reid23/yet-another-pompfen-store/build/components/guard_epp.dxf

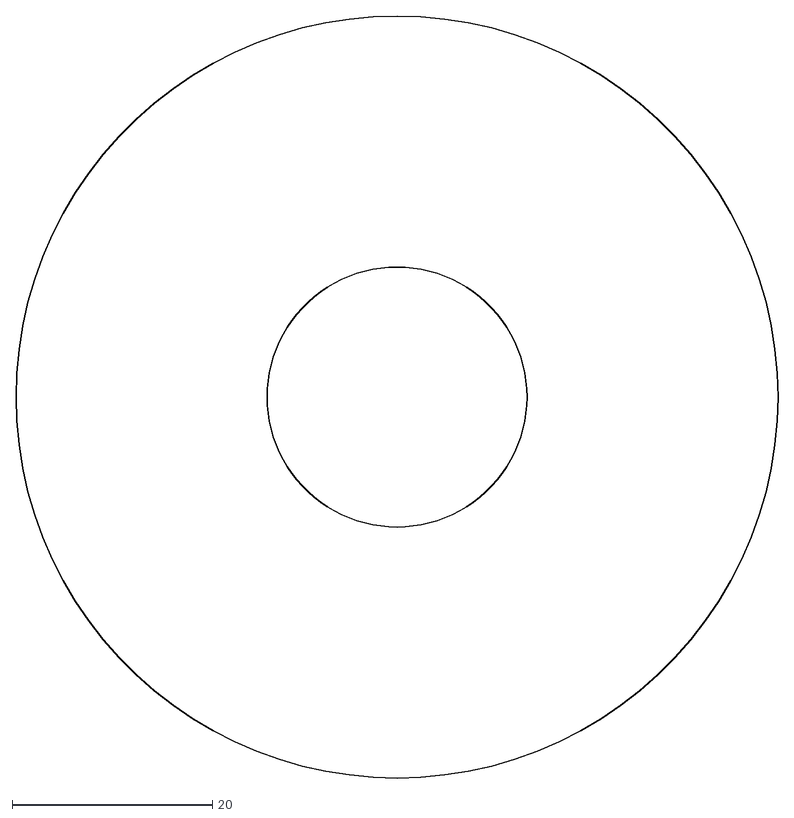
[picture p41: CAD file, 2026-06-17]
build/components/guard_epp.dxf
76.2 x 76.2
