reid23/yet-another-pompfen-store/build/components/tip_cap.stl

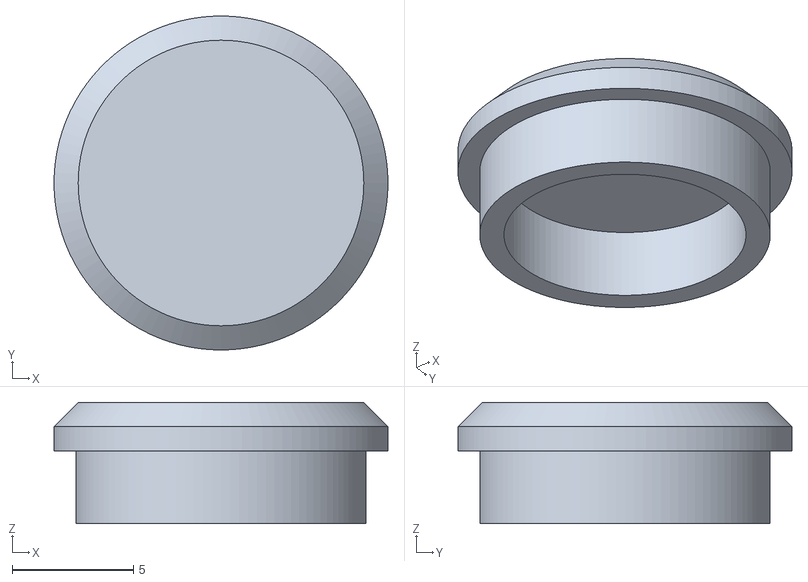
[picture p42: CAD file, 2026-06-17]
build/components/tip_cap.stl
13.8 x 13.8 x 5.00
