reid23/yet-another-pompfen-store/build/extras/guard_collet.stl

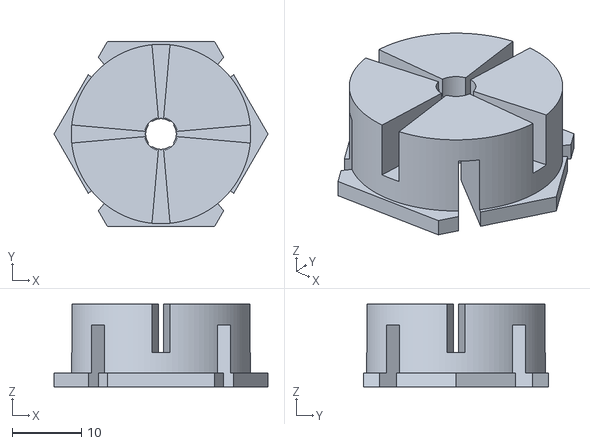
[picture p43: CAD file, 2026-07-21]
build/extras/guard_collet.stl
31.0 x 26.8 x 12.0
