reid23/yet-another-pompfen-store/build/components/blade_epp_foamside.dxf

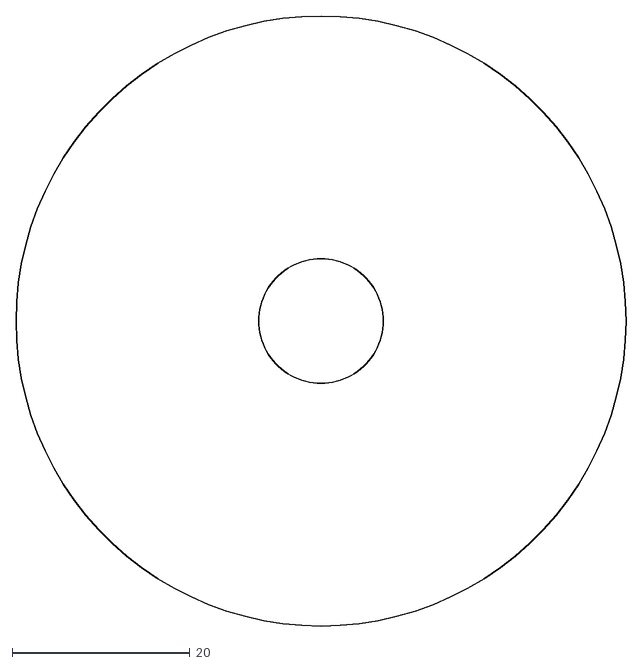
[picture p44: CAD file, 2026-06-17]
build/components/blade_epp_foamside.dxf
68.6 x 68.6
