reid23/yet-another-pompfen-store/build/extras/blade_foamside_collet.stl

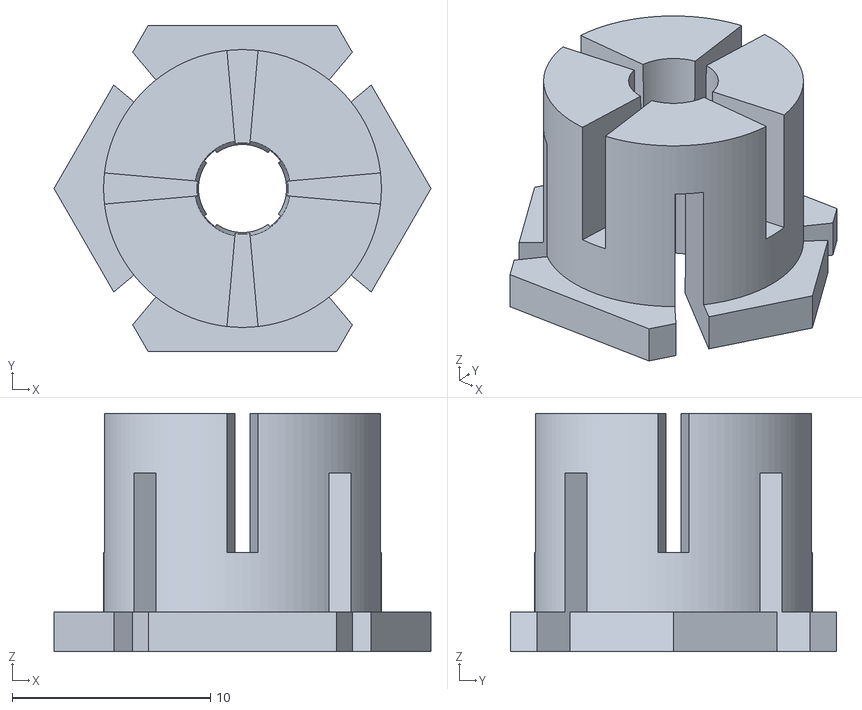
[picture p45: CAD file, 2026-07-21]
build/extras/blade_foamside_collet.stl
19.0 x 16.5 x 12.0
