reid23/yet-another-pompfen-store/build/components/tip_epp_radial.dxf

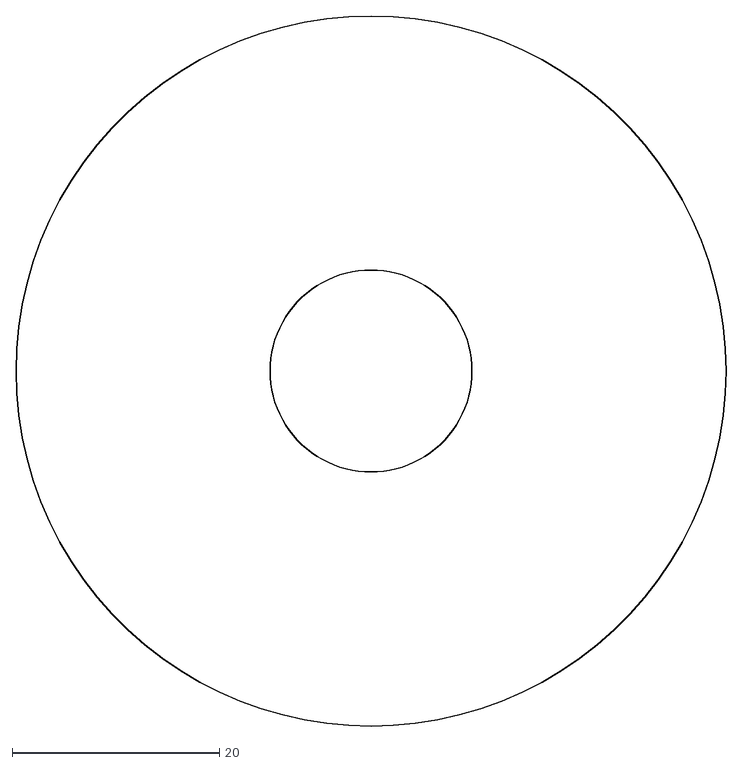
[picture p46: CAD file, 2026-06-17]
build/components/tip_epp_radial.dxf
68.6 x 68.6
