reid23/yet-another-pompfen-store/build/extras/fatigue_jig_bumper.stl

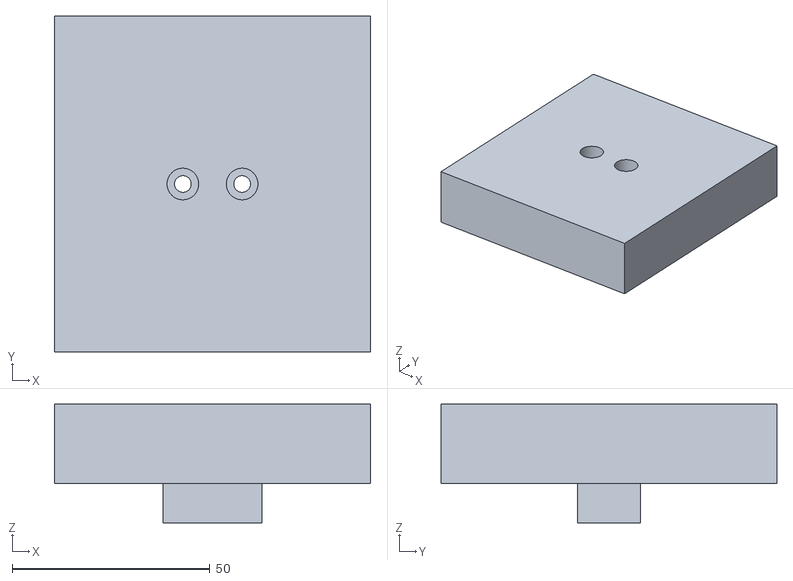
[picture p47: CAD file, 2026-07-21]
build/extras/fatigue_jig_bumper.stl
80.0 x 85.0 x 30.0
