reid23/yet-another-pompfen-store/build/components/collet.stl

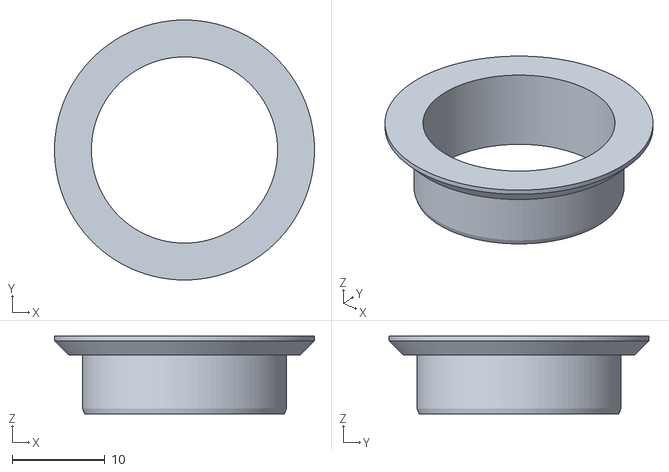
[picture p48: CAD file, 2026-06-17]
build/components/collet.stl
28.0 x 28.0 x 8.35
