reid23/yet-another-pompfen-store/build/extras/fatigue_jig_sample_mount.stl

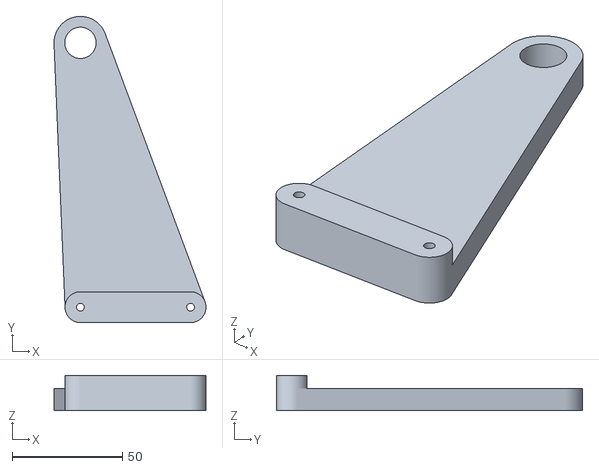
[picture p49: CAD file, 2026-07-21]
build/extras/fatigue_jig_sample_mount.stl
69.0 x 139.0 x 16.0
