reid23/yet-another-pompfen-store/build/components/tip_epp_axial.dxf

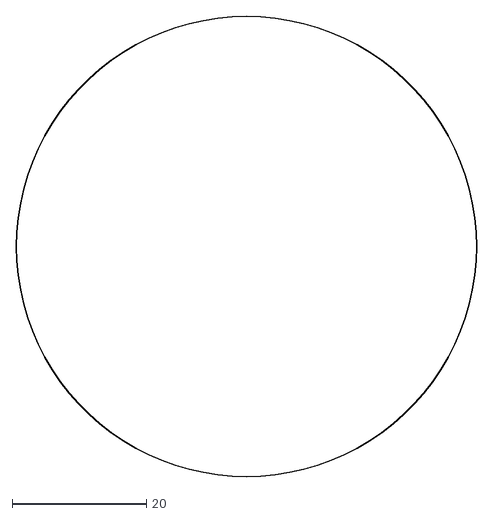
[picture p50: CAD file, 2026-06-17]
build/components/tip_epp_axial.dxf
68.6 x 68.6
