reid23/yet-another-pompfen-store/build/extras/tip_collet.stl

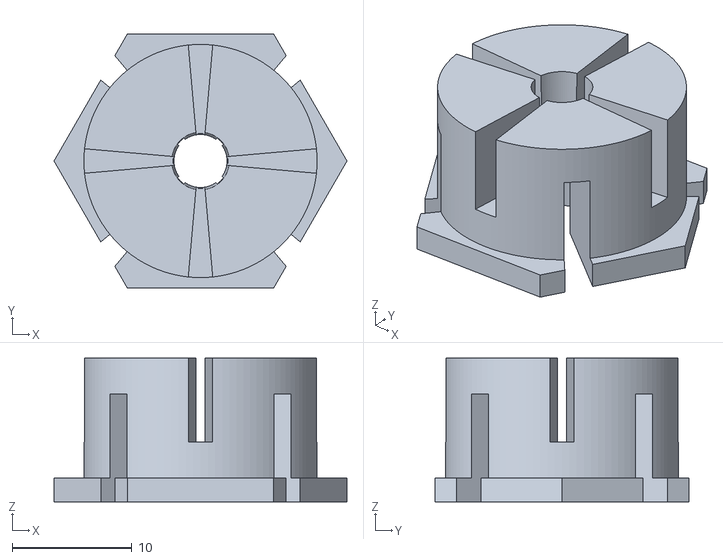
[picture p51: CAD file, 2026-07-21]
build/extras/tip_collet.stl
24.5 x 21.2 x 12.0
