reid23/yet-another-pompfen-store/build/components/pommel.stl

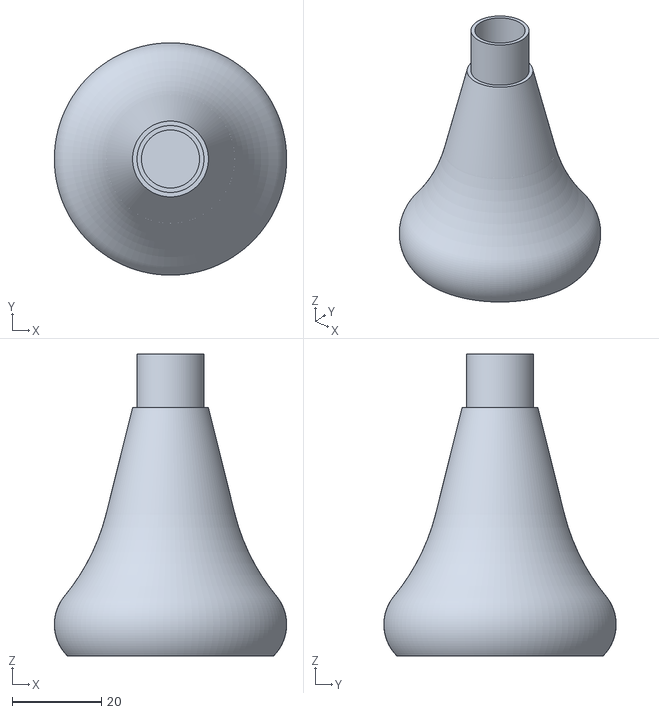
[picture p52: CAD file, 2026-03-15]
build/components/pommel.stl
52.1 x 52.1 x 67.7
