reid23/yet-another-pompfen-store/build/extras/fatigue_jig_strain_guage_mount.stl

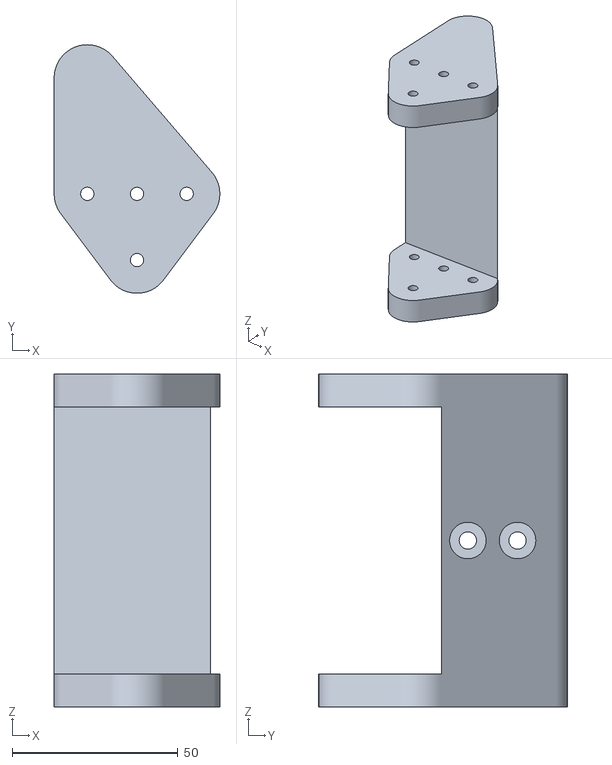
[picture p53: CAD file, 2026-07-21]
build/extras/fatigue_jig_strain_guage_mount.stl
50.0 x 75.0 x 100.5
