reid23/yet-another-pompfen-store/build/components/staff_grip.stl

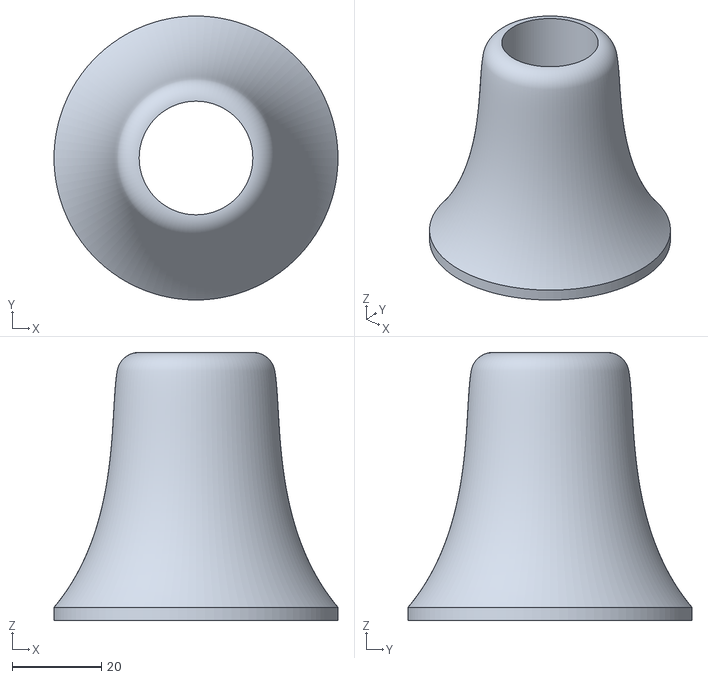
[picture p54: CAD file, 2026-02-28]
build/components/staff_grip.stl
63.5 x 63.5 x 60.0
