reid23/yet-another-pompfen-store/build/extras/blade_handside_collet.stl

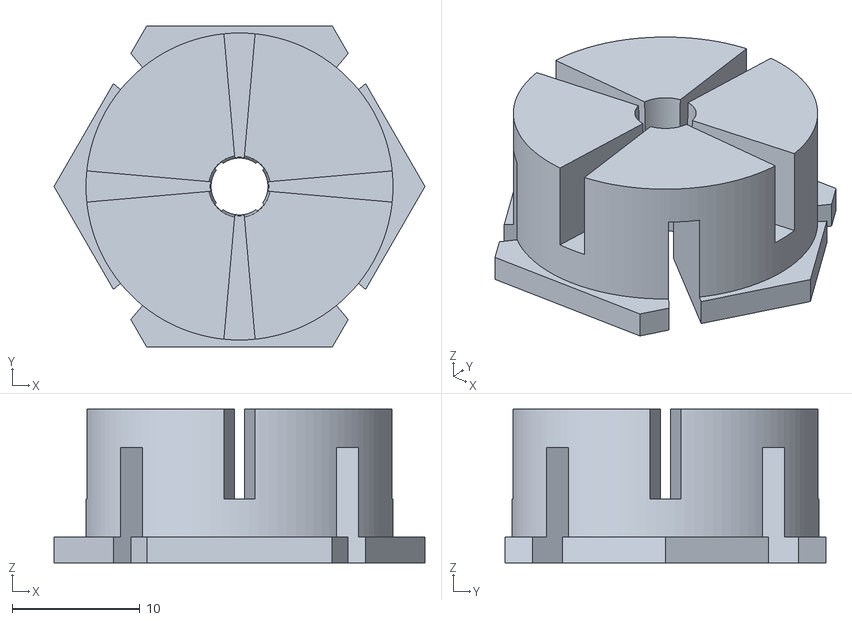
[picture p55: CAD file, 2026-07-21]
build/extras/blade_handside_collet.stl
29.0 x 25.1 x 12.0
