reid23/yet-another-pompfen-store/build/components/staff_grip_narrow.stl

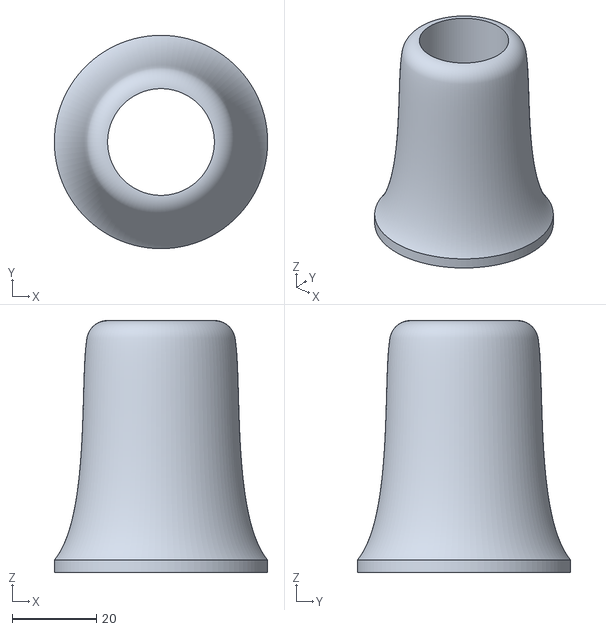
[picture p56: CAD file, 2026-02-28]
build/components/staff_grip_narrow.stl
50.8 x 50.8 x 60.0
