reid23/yet-another-pompfen-store/build/extras/fatigue_jig_encoder_mount.stl

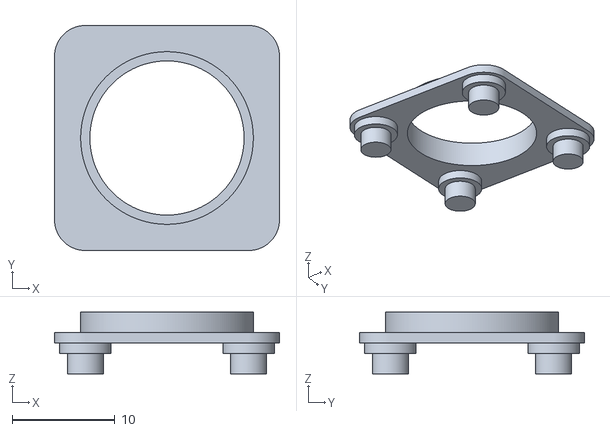
[picture p57: CAD file, 2026-07-21]
build/extras/fatigue_jig_encoder_mount.stl
21.9 x 21.9 x 6.00
