reid23/yet-another-pompfen-store/build/components/pommel_modifier.stl

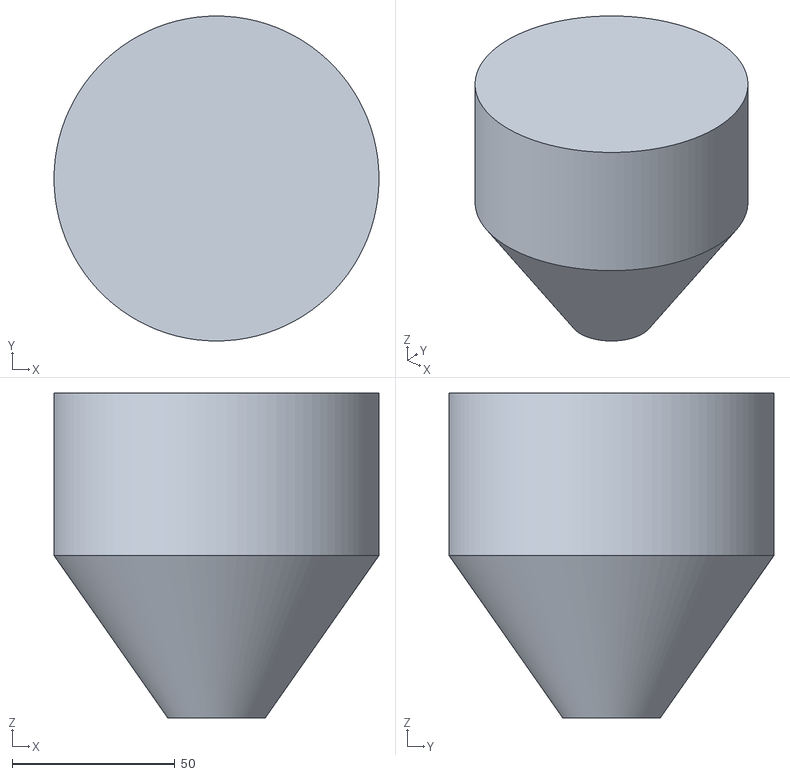
[picture p58: CAD file, 2026-02-24]
build/components/pommel_modifier.stl
100.0 x 100.0 x 100.0
