reid23/yet-another-pompfen-store/build/extras/epp_support_wide_guard.stl

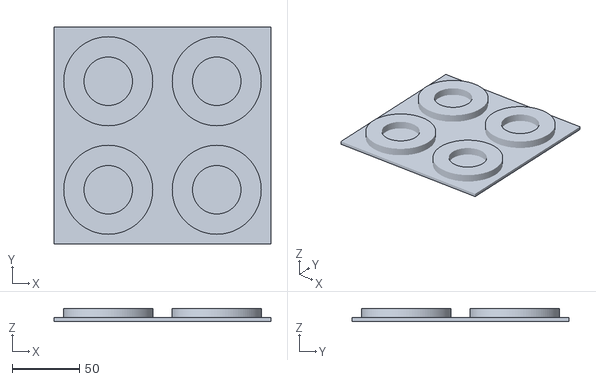
[picture p59: CAD file, 2026-06-17]
build/extras/epp_support_wide_guard.stl
161.4 x 161.4 x 10.0
