reid23/yet-another-pompfen-store/build/components/tip_flange.stl

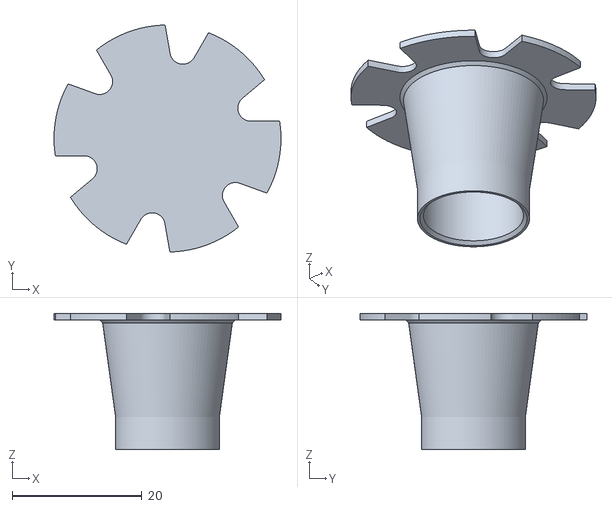
[picture p60: CAD file, 2026-02-24]
build/components/tip_flange.stl
35.0 x 35.0 x 21.0
