reid23/yet-another-pompfen-store/build/extras/tip_clamp_jig.stl

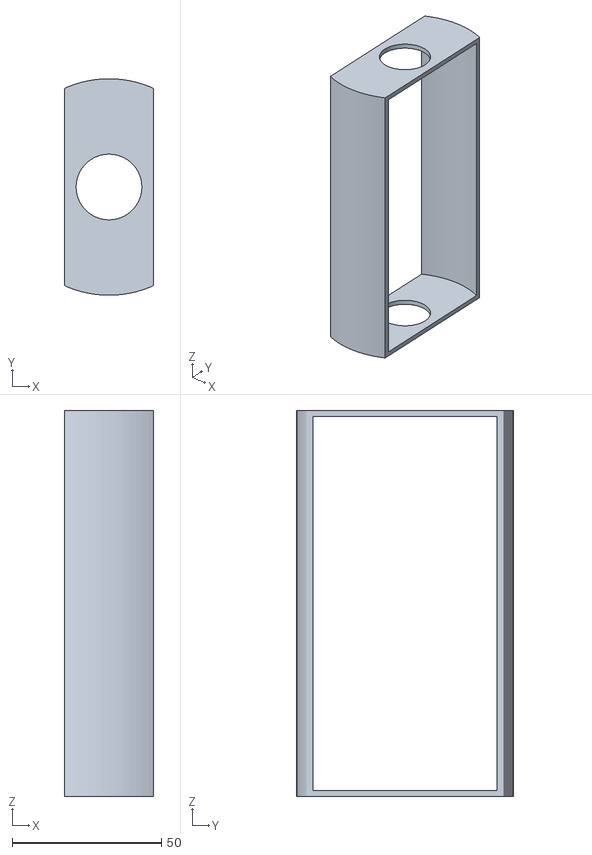
[picture p61: CAD file, 2026-06-17]
build/extras/tip_clamp_jig.stl
30.0 x 72.6 x 129.4
