reid23/yet-another-pompfen-store/build/components/staff_guard_spacer.stl

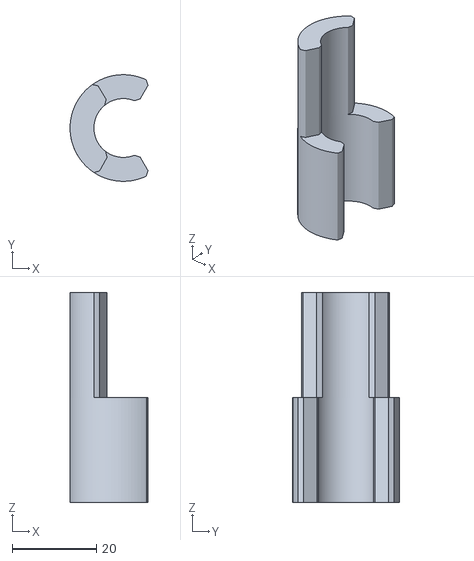
[picture p62: CAD file, 2025-09-28]
build/components/staff_guard_spacer.stl
18.5 x 25.4 x 50.0
