reid23/yet-another-pompfen-store/build/extras/epp_support_narrow_guard.stl

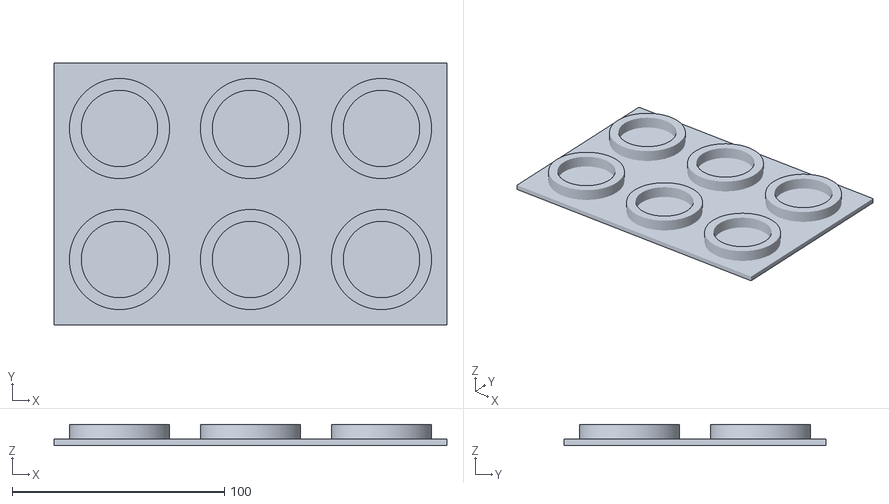
[picture p63: CAD file, 2026-06-17]
build/extras/epp_support_narrow_guard.stl
184.9 x 123.3 x 10.0
