reid23/yet-another-pompfen-store/build/components/staff_spacer.stl

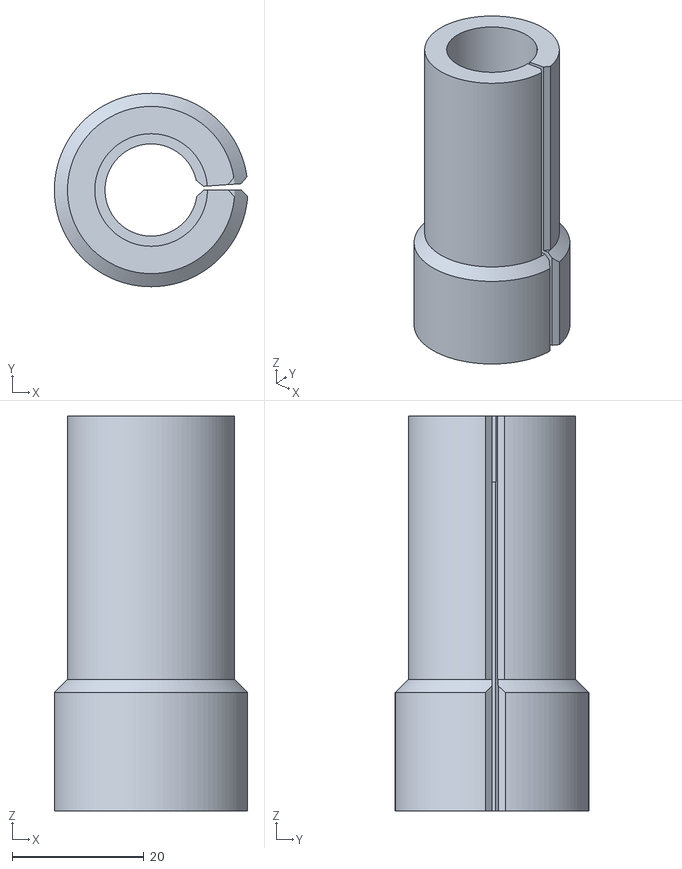
[picture p64: CAD file, 2025-09-28]
build/components/staff_spacer.stl
29.4 x 29.4 x 60.0
