reid23/yet-another-pompfen-store/build/extras/epp_support_blade.stl

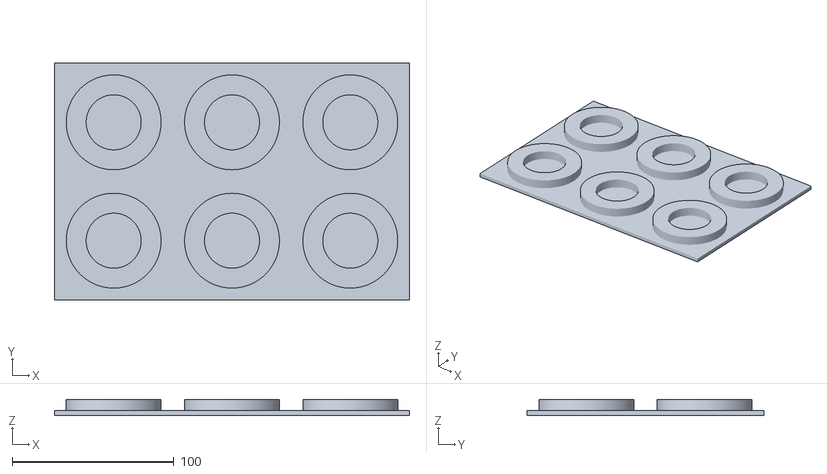
[picture p65: CAD file, 2026-02-08]
build/extras/epp_support_blade.stl
219.2 x 146.2 x 10.0
