reid23/yet-another-pompfen-store/foam.scad

include <BOSL2/std.scad>
include <params.scad>

module tip_noodle(
    anchor=CENTER,
    spin=0,
    orient=UP){
    anchors = [
        named_anchor(name="tip_noodle_bottom", pos=CENTER, orient=DOWN),
        named_anchor(name="tip_noodle_top", pos=(TIP_THICKNESS-EPP_THICKNESS)*UP, orient=UP)
    ];
    attachable(anchor, spin, orient, anchors=anchors){
        zcyl(h=TIP_THICKNESS-EPP_THICKNESS, d=NOODLE_OD, anchor=BOTTOM);
        children();
    }
}

module blade_noodle(raw_length,
    anchor=CENTER,
    spin=0,
    orient=UP){
    anchors = [
        named_anchor(name="core_tip", pos=raw_length*UP, orient=UP),
        named_anchor(name="hand_side", pos=CENTER, orient=DOWN)
    ];
    attachable(anchor, spin, orient, anchors=anchors){
        tube(h=raw_length, od=NOODLE_OD, id=SHEEP_DIAMETER, anchor=BOTTOM);
        children();
    }
}

module buffer_noodle(
    anchor=CENTER,
    spin=0,
    orient=UP){
    anchors = [
        named_anchor(name="buffer_top", pos=BUFFER_THICKNESS*UP, orient=UP),
        named_anchor(name="buffer_bottom", pos=CENTER, orient=UP)
    ];

    attachable(anchor, spin, orient, anchors=anchors){
        tube(h=BUFFER_THICKNESS, od=NOODLE_OD, id=SHEEP_DIAMETER, anchor=BOTTOM);
        children();
    }
}
module guard_foam(
    od, total_length,
    anchor=CENTER,
    spin=0,
    orient=UP){
    length = total_length - 2*EPP_THICKNESS - STAFF_GRIP_HEIGHT - 2; // -2 is for gap between EPP and grip
    anchors = [
        named_anchor(name="guard_foam_top", pos=UP*length),
        named_anchor(name="guard_foam_bottom", pos=CENTER),
        named_anchor(name="guard_foam_center", pos=UP*(length/2+EPP_THICKNESS/2))
    ];
    attachable(anchor, spin, orient, anchors=anchors){
        tube(h=length, od=od, id=INCH, anchor=BOTTOM);
        children();
    }
}
