reid23/yet-another-pompfen-store/utils.scad

include <BOSL2/std.scad>

module debuggable(c=undef, split_anchor=undef, split_orient=undef){
  difference(){
    if(!is_undef(c)){
      color(c) union() children();
    } else {
      union() children();
    }
    if(!is_undef(split_anchor) && !is_undef(split_orient)){
      // ? figure out some way to make a plane
    }
  }
}

module pleb_debug(c) {
  color(c) difference(){
    union() { children(); }
    cube(1000, anchor=RIGHT);
  }
}

function hermite(t, p0, p1, v0, v1) = (
    [[t*t*t, t*t, t, 1]]
  * [[2, -2, 1, 1], 
     [-3, 3, -2, -1], 
     [0, 0, 1, 0], 
     [1, 0, 0, 0]]
  * [p0,p1,v0,v1]
)[0];

function rad2deg(x) = x*180/3.14159265358979;
function cos_sin(theta) = [cos(theta), sin(theta)];

module _chamfered_slotted_ring(ir, or, slot_angular_size, chamfer_size){
    startsideangles = [
        -rad2deg(chamfer_size/ir), 
        0.0, 
        0.0, 
        -rad2deg(chamfer_size/or)
    ];
    endsideangles   = [
        slot_angular_size+rad2deg(chamfer_size/or),
        slot_angular_size, 
        slot_angular_size, 
        slot_angular_size+rad2deg(chamfer_size/ir)
    ];
    difference(){
        circle(r=or);
        circle(r=ir);
        polygon(concat(
            [[0, 0]], 
            [for(i=[0:1:slot_angular_size]) 2*or*cos_sin(i)],
            [2*or*cos_sin(slot_angular_size)]
        ));

        // polygon([[0, 0], 2*or*[1, 0], 2*or*[cos(slot_angular_size), sin(slot_angular_size)]]);
        polygon([
            cos_sin(startsideangles[0])     * ir,
            cos_sin(startsideangles[1])     * (ir+chamfer_size),
            cos_sin(startsideangles[2])     * (or-chamfer_size),
            cos_sin(startsideangles[3])     * or,
            cos_sin(startsideangles[3])     * or*2,
            cos_sin(startsideangles[2])     * or*2,
            cos_sin(startsideangles[1])     * (ir-chamfer_size)
        ]);
        polygon([
            cos_sin(endsideangles[2])       * (ir-chamfer_size),
            cos_sin(endsideangles[1])       * 2*or,
            cos_sin(endsideangles[0])       * 2*or,
            cos_sin(endsideangles[0])       * or,
            cos_sin(endsideangles[1])       * (or-chamfer_size),
            cos_sin(endsideangles[2])       * (ir+chamfer_size),
            cos_sin(endsideangles[3])       * ir,
        ]);
    }
}
module radially_distributed_filleted_slots(ir, r_fillet=2, theta=40, n=6){
    x = r_fillet/tan(theta/2);
    offset_rad = ir - (sqrt(x*x + r_fillet*r_fillet)-r_fillet);
    for(i=[0:(360/n):360]) zrot(i) translate(offset_rad*[cos(theta/2), sin(theta/2), 0]) {
        down(50) linear_extrude(height = 100) union() {
            polygon([
                [x, 0],
                [100, 0],
                100*[cos(theta), sin(theta)],
                x*[cos(theta), sin(theta)],
            ]);
            translate([x, r_fillet, 0]) circle(r_fillet);
        }
    }
}
